giomf/AM03127-Controller/kiCad/ff-led-panel/ff-led-panel.kicad_sch

## KiCad design kiCad/ff-led-panel/ff-led-panel.kicad_sch (2025-08-29)

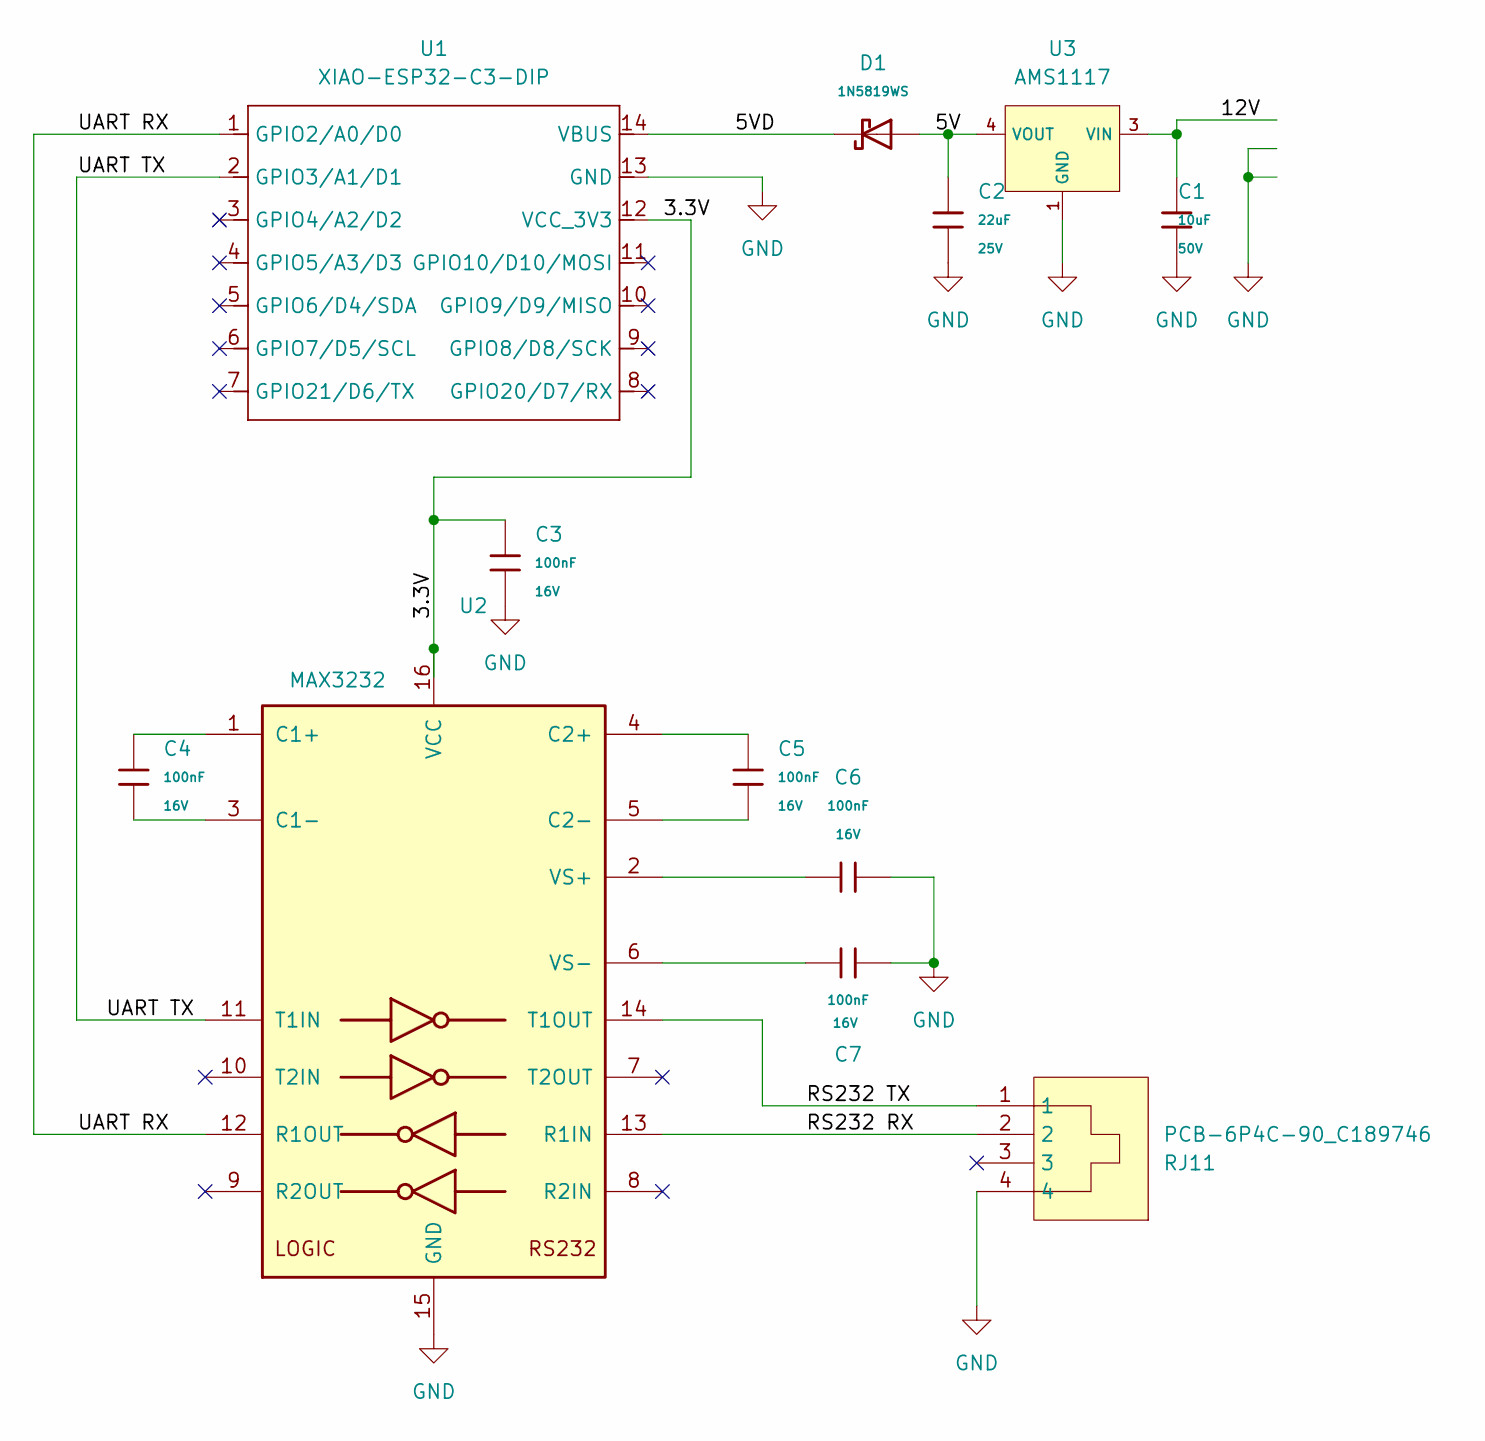
[picture p3: schematic ff-led-panel.kicad_sch]

Parts:
C1: 10uF; C_1206; Voltage Rated 50V; Tolerance ±10%; Part CL31A106KBHNNNE; LCSC C13585
C2: 22uF; C_1206; Voltage Rated 25V; Tolerance ±10%; Part CL31A226KAHNNNE; LCSC C12891
C3, C4, C5, C6, C7: 100nF; C_0402; Voltage Rated 16V; Tolerance ±10%; Part CL05B104KO5NNNC; LCSC C1525
D1: 1N5819WS; D_SOD-323; Forward Voltage (Vf@If) 600mV@1A; Reverse Voltage (Vr) 40V; Part 1N5819WS; LCSC C191023
RJ11: PCB-6P4C-90_C189746; RJ11-TH_PCB-6P4C-90_C189746; LCSC Part C189746
U1: XIAO-ESP32-C3-DIP; XIAO-ESP32C3-DIP
U2: MAX3232; SOIC-16_3.9x9.9mm_P1.27mm
U3: AMS1117; SOT-223_L6.5-W3.5-P2.30-LS7.0-BR; Output Voltage 5V; Dropout Voltage 1.3V@(1A); Part AMS1117-5.0; LCSC C6187

Connections:
3.3V: C3.1, U1.12 (VCC_3V3), U2.16 (VCC)
5V: C2.1, D1.2, U3.2 (VOUT), U3.4 (VOUT)
5VD: D1.1, U1.14 (VBUS)
12V: C1.1, U3.3 (VIN)
GND: C1.2, C2.2, C3.2, C6.2, C7.2, RJ11.4, U1.13 (GND), U2.15 (GND), U3.1 (GND)
unnamed: C4.1, U2.1 (C1+)
unnamed: C4.2, U2.3 (C1-)
unnamed: C5.1, U2.4 (C2+)
unnamed: C5.2, U2.5 (C2-)
unnamed: C6.1, U2.2 (VS+)
unnamed: C7.1, U2.6 (VS-)
RS232 RX: RJ11.2, U2.13 (R1IN)
RS232 TX: RJ11.1, U2.14 (T1OUT)
UART RX: U1.1 (GPIO2/A0/D0), U2.12 (R1OUT)
UART TX: U1.2 (GPIO3/A1/D1), U2.11 (T1IN)
