giomf/AM03127-Controller/am03127-cli/src/commands/open.rs

use anyhow::{Context, Result};

use crate::config::Panel;

pub fn run(panel: &Panel) -> Result<()> {
    let url = format!("http://{}", panel.address);

    println!("Opening {} ...", url);

    std::process::Command::new("xdg-open")
        .arg(&url)
        .status()
        .with_context(|| format!("failed to open '{url}'"))?;

    Ok(())
}
