giomf/AM03127-Controller/am03127-firmware/build.rs

fn main() {
    emit_build_time();
    emit_build_version();
    linker_be_nice();
    // make sure linkall.x is the last linker script (otherwise might cause problems with flip-link)
    println!("cargo:rustc-link-arg=-Tlinkall.x");
}

fn emit_build_version() {
    println!("cargo:rerun-if-changed=.git/HEAD");
    println!("cargo:rerun-if-changed=.git/refs/heads");
    println!("cargo:rerun-if-env-changed=FORCE_VERSION_REBUILD");

    let hash = std::process::Command::new("git")
        .args(["rev-parse", "--short", "HEAD"])
        .output()
        .ok()
        .filter(|o| o.status.success())
        .and_then(|o| String::from_utf8(o.stdout).ok())
        .map(|s| s.trim().to_string())
        .unwrap_or_else(|| "unknown".to_string());

    let dirty = std::process::Command::new("git")
        .args(["status", "--porcelain"])
        .output()
        .ok()
        .filter(|o| o.status.success())
        .map(|o| !o.stdout.is_empty())
        .unwrap_or(false);

    let version = if dirty {
        format!("{hash}-dirty")
    } else {
        hash
    };

    println!("cargo:rustc-env=BUILD_VERSION={version}");
}

fn emit_build_time() {
    let now = time::OffsetDateTime::now_utc();
    println!(
        "cargo:rustc-env=BUILD_TIME={:02}:{:02}:{:02}",
        now.hour(),
        now.minute(),
        now.second()
    );
    println!(
        "cargo:rustc-env=BUILD_DATE={}-{:02}-{:02}",
        now.year(),
        now.month() as u8,
        now.day()
    );
}

fn linker_be_nice() {
    let args: Vec<String> = std::env::args().collect();
    if args.len() > 1 {
        let kind = &args[1];
        let what = &args[2];

        match kind.as_str() {
            "undefined-symbol" => match what.as_str() {
                "_defmt_timestamp" => {
                    eprintln!();
                    eprintln!(
                        "💡 `defmt` not found - make sure `defmt.x` is added as a linker script and you have included `use defmt_rtt as _;`"
                    );
                    eprintln!();
                }
                "_stack_start" => {
                    eprintln!();
                    eprintln!("💡 Is the linker script `linkall.x` missing?");
                    eprintln!();
                }
                _ => (),
            },
            // we don't have anything helpful for "missing-lib" yet
            _ => {
                std::process::exit(1);
            }
        }

        std::process::exit(0);
    }

    println!(
        "cargo:rustc-link-arg=--error-handling-script={}",
        std::env::current_exe().unwrap().display()
    );
}
